Gabko11111111/OpenPi-Laptop/CAD/v0.2/STL/lid_back.stl

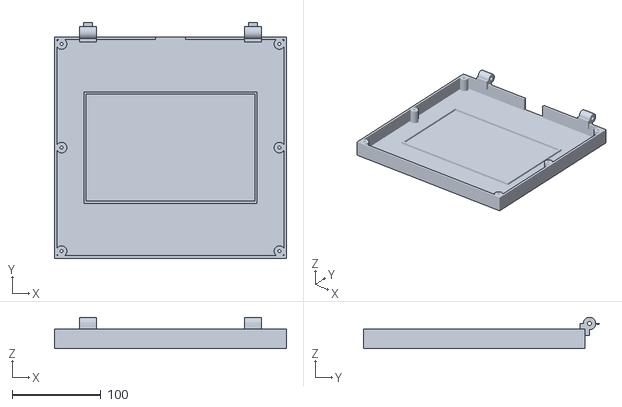
[picture p17: CAD file, 2026-09-13, an earlier design]
CAD/v0.2/STL/lid_back.stl
262.0 x 266.0 x 35.5
