Gabko11111111/OpenPi-Laptop/CAD/v0.2/STL/display_bezel.stl

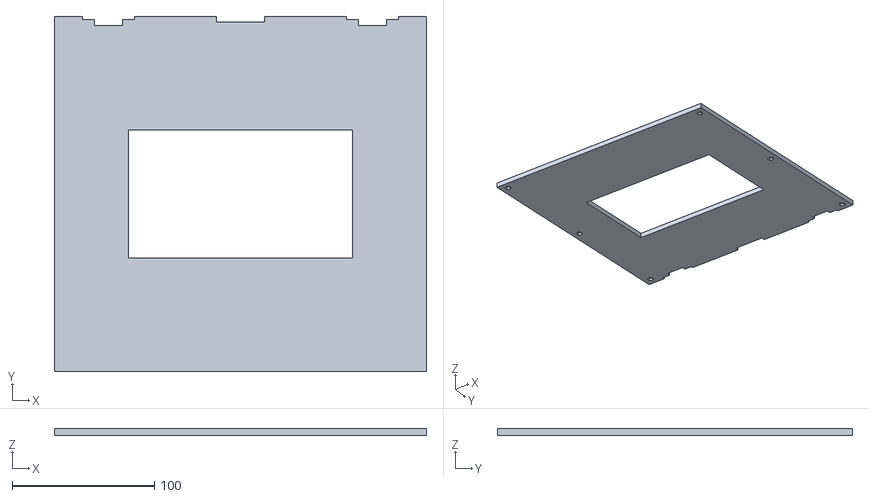
[picture p18: CAD file, 2026-09-13, an earlier design]
CAD/v0.2/STL/display_bezel.stl
262.0 x 250.0 x 5.00
